balmerdx/Microampermeter/py/view_data.py

#!/usr/bin/env python3
import array
import math
import cmath
import sys
from os.path import splitext
import matplotlib.pyplot as plt
from struct import iter_unpack
from scipy.fftpack import fft
import scipy as np
from sys import argv
from scipy import signal
import xml.etree.ElementTree as ET

TIME_STEP = 1/105.46e3

def makeTimeList(readableData, xmin, xstep):
	N = len(readableData)
	return np.linspace(start = xmin, stop = xstep*(N-1), num = N)

def ToIntFrom24bit(d):
	d = d & 0xFFFFFF
	if d < 0x800000:
		return d
	return d-0x1000000

def readDataInt(filename, na):
	'''
		na = nanoamter format
	'''
	data_x = []
	data_y = []
	f = open(filename, "rb")
	data = f.read()
	f.close()

	if na:
		for (x,y) in iter_unpack("ii", data):
			data_x.append(x)
			data_y.append(y)
	else:
		for (x,y) in iter_unpack("II", data):
			data_x.append(ToIntFrom24bit(x))
			data_y.append(ToIntFrom24bit(y))
	return (data_x, data_y)

def readDataFloat(filename):
	'''
		na = nanoamter format
	'''
	data_x = []
	f = open(filename, "rb")
	data = f.read()
	f.close()

	for x in iter_unpack("f", data):
		data_x.append(x[0])
	return np.asarray(data_x, dtype=np.float32)


def readData(filename, na):
	(data_x, data_y) = readDataInt(filename, na)
	if na:
		mul_x = 1e-3 #nA -> µA
		return (np.asarray(data_x, dtype=np.float32)*mul_x, np.asarray(data_y, dtype=np.int32))
	else:
		mul_x = 1./(2**22)
		mul_y = mul_x
		return (np.asarray(data_x, dtype=np.float32)*mul_x, np.asarray(data_y, dtype=np.float32)*mul_y)
	pass

def plotXY(data_x, data_y = None, xlabel = "T(ms)"):
	fig, ax = plt.subplots()

	timeList = makeTimeList(data_x, 0, TIME_STEP*1e3)
	#timeList = makeTimeList(data_x, 0, 1)

	if xlabel:
		ax.set_xlabel(xlabel)
	ax.plot(timeList, data_x, color='red')
	if data_y:
		ax.plot(timeList, data_y, color='blue')
	plt.show()

def plotColors(data_x, data_y, xlabel = "T(ms)", ylabel="I(µA)"):
	fig, ax = plt.subplots()

	timeList = makeTimeList(data_x, 0, TIME_STEP*1e3)
	#timeList = makeTimeList(data_x, 0, 1)

	if xlabel:
		ax.set_xlabel(xlabel)
	if ylabel:
		ax.set_ylabel(ylabel)

	colors = ['red', 'green', 'blue', 'black', 'orange']

	cur_y = data_y[0]
	start_i = 0
	for i in range(len(timeList)):
		if data_y[i]!=cur_y:
			end_i= i+1
			print(len(timeList), start_i, end_i, cur_y)
			if cur_y==255:
				cur_y = 4

			ax.plot(timeList[start_i:end_i], data_x[start_i:end_i], ".", color=colors[cur_y])
			start_i = i
			cur_y = data_y[i]

	if start_i < len(timeList):
		ax.plot(timeList[start_i:len(timeList)], data_x[start_i:len(timeList)], '.', color=colors[cur_y])
		pass

	plt.show()

def removeAverage(data):
	x = np.average(data)
	return np.subtract(data, x)


def makeFFT(data):
	N = len(data)
	yf = fft(data)
	yf_abs = 2.0/N * np.absolute(yf[0:N//2])
	yf_dbfs = 20 * np.log10(yf_abs)
	ref_db = 0
	yf_dbfs = np.subtract(yf_dbfs, ref_db)
	xf = np.linspace(0.0, 1.0/(2.0*TIME_STEP), N//2)
	return (xf, yf_dbfs)


def plotFFT(data, color = 'blue'):
	window = signal.blackman(len(data))
	(xf, yf) = makeFFT(data * window)

	fig, ax = plt.subplots()
	ax.set_xlabel('F (Hz)')
	ax.set_ylabel('dB(fft)')
	ax.set_ylim(bottom=-120, top=0)
	#ax.set_ylim(bottom=-120, top=-60)
	ax.plot(xf, yf, color=color)
	plt.grid()
	plt.show()

def plotFFT2(data1, data2):
	(xf1, yf1) = makeFFT(data1)
	(xf2, yf2) = makeFFT(data2)

	fig, ax = plt.subplots()
	ax.set_xlabel('F (Hz)')
	ax.set_ylabel('dB(fft)')
	ax.set_ylim(bottom=-120, top=0)
	ax.plot(xf1, yf1, color='red')
	ax.plot(xf2, yf2, color='blue')
	plt.grid()
	plt.show()

def checkBits(data, text):
	#ищем неизменные биты.
	#если бит не изменяется - это косяк
	#не работает эта проверка, не всегда бит 

	bits_and = 0xFFFF
	bits_or = 0
	for x in data:
		bits_and = bits_and & x
		bits_or = bits_or | x

	for i in range(32):
		if (bits_and & (1<<i)):
			print(text, ": bit", i, " is 1 permanently")
		if (bits_or & (1<<i))==0:
			print(text, ": bit", i, " is 0 permanently")
	return
'''
def colorFixData(data_x, data_y):
	#В data_y у нас резисторы для переключения.
	#Мы некоторое количество данных делим на k (так как от старого резистора значения)
	n_div = 47
	k_div = 0
	k_mul = 0.1
	prev_y = data_y[0]
	for i in range(len(data_x)):
		if prev_y!=data_y[i]:
			prev_y = data_y[i]
			k_div = n_div
		if k_div>0:
			k_div = k_div-1
			data_x[i] *= k_mul
			if k_div==6:
				data_x_last = data_x[i]
			if k_div<6:
				data_x[i] = data_x_last

	pass
'''


def ViewDataBin(filename, na):
	'''
	(data_xi, data_yi) = readDataInt(filename, na)
	big = 100000
	for i in range(len(data_xi)-100, len(data_xi)):
	#for i in range(len(data_xi)):
		xi = data_xi[i]
		yi =  data_yi[i]
		#if xi<-big or xi>big or yi<-big or yi>big:
		#	print(i, xi, yi)
		print(i, xi, yi)

	
	#checkBits(data_xi, "X")
	#checkBits(data_yi, "Y")
	return
	'''

	(data_x, data_y) = readData(filename, na)

	print(len(data_x), len(data_y))
	if na:
		#colorFixData(data_x, data_y)
		plotColors(data_x, data_y)
		#plotXY(data_x)
		return
	#print(data_x[0], data_y[0])

	#data_x = removeAverage(data_x)
	#data_y = removeAverage(data_y)
	plotXY(data_x, data_y)
	#plotXY(data_x)
	#plotXY(data_y)
	#plotFFT(data_x, color = 'red')
	#plotFFT(data_y, color = 'blue')
	#plotFFT2(data_x, data_y)

def ViewDataBinFloat(filename):
	data_x = readDataFloat(filename)
	#data_y = makeTimeList(data_x, xmin=0, xstep=1/105468.75)
	#print(data_x[0])
	#print(len(data_x))
	plotXY(data_x)


if len(sys.argv)>1:
	filename = sys.argv[1]
else:
	filename = "out.a"

ext = splitext(filename)[1]
print("ext=", ext)
if ext == ".bin":
	ViewDataBin(filename, na = False)
if ext == ".na":
	ViewDataBin(filename, na = True)
if ext == ".a":
	ViewDataBinFloat(filename)
