balmerdx/Microampermeter/h7code/Core/Src/measure/calculate.h

#pragma once

typedef struct
{
    float Vout;
    float current;
    float resistance;
    bool infinity_resistance;
} CalcResult;


void CorrectionInit();

float calculateCurrent(int32_t measureI, float RshuntInv);

float calculateVoltage(int32_t measureV);
float calculateShuntVoltage(int32_t measureI);

void calculateRV(float voltage, float current,
               float Rshunt, CalcResult* calc_result);
