balmerdx/Microampermeter/h7code/Core/Src/hardware/ADS1271_input.c

#include "stm32h7xx_hal.h"
#include "ADS1271_input.h"
#include "delay.h"

#define ADS1271_MODE_PORT GPIOE
#define ADS1271_MODE_PIN GPIO_PIN_3

#define ADS1271_NOT_PDWN_PORT GPIOE
#define ADS1271_NOT_PDWN_PIN GPIO_PIN_1

float ADS1271_SPS = 27e6f/256;

#define AUDIO_BUFFER_SIZE (ADS1271_RECEIVE_DATA_SIZE*2)
ADS1271_Data audio_buf[ADS1271_RECEIVE_DATA_SIZE*2] __attribute__((section(".d2_data"))) __attribute__ ((aligned (32)));

extern SAI_HandleTypeDef hsai_BlockA1;

void HAL_SAI_RxHalfCpltCallback(SAI_HandleTypeDef *hsai)
{
    (void)hsai;
    SCB_InvalidateDCache_by_Addr((uint32_t*)audio_buf, ADS1271_RECEIVE_DATA_SIZE*sizeof(audio_buf[0]));
    ADS1271_ReceiveData(audio_buf);
}

void HAL_SAI_RxCpltCallback(SAI_HandleTypeDef *hsai)
{
    (void)hsai;
    SCB_InvalidateDCache_by_Addr((uint32_t*)(audio_buf+ADS1271_RECEIVE_DATA_SIZE), ADS1271_RECEIVE_DATA_SIZE*sizeof(audio_buf[0]));
    ADS1271_ReceiveData(audio_buf+ADS1271_RECEIVE_DATA_SIZE);
}

void ADS1271_Init()
{
    GPIO_InitTypeDef  gpio = {};
    gpio.Pull      = GPIO_NOPULL;
    gpio.Speed     = GPIO_SPEED_FREQ_LOW;

    gpio.Mode      = GPIO_MODE_OUTPUT_PP;
    gpio.Pin       = ADS1271_MODE_PIN;
    HAL_GPIO_Init(ADS1271_MODE_PORT, &gpio);

    gpio.Pin       = ADS1271_NOT_PDWN_PIN;
    HAL_GPIO_Init(ADS1271_NOT_PDWN_PORT, &gpio);

    HAL_GPIO_WritePin(ADS1271_MODE_PORT, ADS1271_MODE_PIN, 0);
    HAL_GPIO_WritePin(ADS1271_NOT_PDWN_PORT, ADS1271_NOT_PDWN_PIN, 0);
    DelayMs(200);
    HAL_GPIO_WritePin(ADS1271_NOT_PDWN_PORT, ADS1271_NOT_PDWN_PIN, 1);
    DelayMs(10);
    ADS1271_ReceiveDataInit();
}

void ADS1271_Start()
{
    //*2 так как 2 канала
    HAL_SAI_Receive_DMA(&hsai_BlockA1, (uint8_t*)&audio_buf[0], AUDIO_BUFFER_SIZE*2);
}
