balmerdx/Microampermeter/h7code/Core/Src/hardware/gpios.h

#pragma once

void GpiosInit();

typedef enum RESISTOR
{
    RESISTOR_1_Kom = 0,
    RESISTOR_100_Om,
    RESISTOR_10_Om,
    RESISTOR_1_Om,
} RESISTOR;

void SetResistor(RESISTOR r);
RESISTOR GetResistor();
float GetResistorValue(RESISTOR r);
float GetResistorValueInv(RESISTOR r);


void SetEnableV(bool enable);
