balmerdx/Microampermeter/h7code/Core/Src/gui/menu_oscilloscope.c

#include "main.h"
#include "menu_oscilloscope.h"
#include "menu_switch_scene.h"
#include "menu_trigger_level.h"
#include "menu_bandwidth.h"
#include "scene_oscilloscope.h"

#include "interface/interface.h"
#include "interface/menu.h"
#include "measure/settings.h"

#include <string.h>

enum
{
    MO_SWITCH_TO,
    MO_BANDWIDTH,
    MO_TRIGGER_START,
    MO_TRIGGER_LEVEL,
    MO_TRIGGER_RISING,
    MO_ENCODER_SCALE_CURRENT,
    MO_ENCODER_SCALE_TIME,
    MO_ENCODER_OFFSET_TIME,
};

static void MenuOscilloscopeQuant();

static int last_menu_index = 0;

void MenuOscilloscopeStart()
{
    char str[32];
    MenuReset("Oscilloscope menu");
    MenuAdd("Switch to...", MO_SWITCH_TO);
    MenuAdd("Trigger start", MO_TRIGGER_START);
    strcpy(str, "Trigger level - ");
    strcat(str, TrigerLevelStr(g_settings.trigger_level));
    MenuAdd(str, MO_TRIGGER_LEVEL);
    MenuAdd(g_settings.trigger_rising?"Trigger rising":"Trigger falling", MO_TRIGGER_RISING);
    MenuAdd("Bandwidth", MO_BANDWIDTH);
    MenuAdd("Encoder scale current", MO_ENCODER_SCALE_CURRENT);
    MenuAdd("Encoder scale time", MO_ENCODER_SCALE_TIME);
    MenuAdd("Encoder offset time", MO_ENCODER_OFFSET_TIME);

    MenuSetIndex(last_menu_index);
    MenuRedraw();
    InterfaceGoto(MenuOscilloscopeQuant);
}

void MenuOscilloscopeQuant()
{
    MenuQuant();
    if(!EncButtonPressed())
        return;
    last_menu_index = MenuIndex();

    if(MenuData()==MO_SWITCH_TO)
    {
        MenuSwitchSceneStart();
        return;
    }

    if(MenuData()==MO_BANDWIDTH)
    {
        MenuBandwidthStart();
        return;
    }

    if(MenuData()==MO_TRIGGER_START)
    {
        OscilloscopeTriggerStart();
        SceneOscilloscopeStart();
        return;
    }

    if(MenuData()==MO_TRIGGER_LEVEL)
    {
        MenuTriggerLevelStart();
        return;
    }

    if(MenuData()==MO_TRIGGER_RISING)
    {
        g_settings.trigger_rising = g_settings.trigger_rising ? 0 : 1;
        SaveSettings();
        MenuOscilloscopeStart();
        return;
    }

    if(MenuData()==MO_ENCODER_SCALE_CURRENT)
    {
        SetOscilloscopeEncoder(ENCODER_SCALE_CURRENT);
        SceneOscilloscopeStart();
        return;
    }

    if(MenuData()==MO_ENCODER_SCALE_TIME)
    {
        SetOscilloscopeEncoder(ENCODER_SCALE_TIME);
        SceneOscilloscopeStart();
        return;
    }

    if(MenuData()==MO_ENCODER_OFFSET_TIME)
    {
        SetOscilloscopeEncoder(ENCODER_OFFSET_TIME);
        SceneOscilloscopeStart();
        return;
    }
}
