balmerdx/Microampermeter/h7code/Core/Src/gui/menu_switch_scene.h

#pragma once
void MenuSwitchSceneStart();

typedef enum SwitchToEnum
{
    SWITCH_TO_MICROAMPERMETER = 0,
    SWITCH_TO_HISTOGRAM = 1,
    SWITCH_TO_OSCILLOSCOPE = 2,
    _MAX_SWITCH_TO,
} SwitchToEnum;

void SwitchToScene(SwitchToEnum data);
